rrbutani/glowing-potato/hardware/boards/pico/revA/img/pico-bottom.png

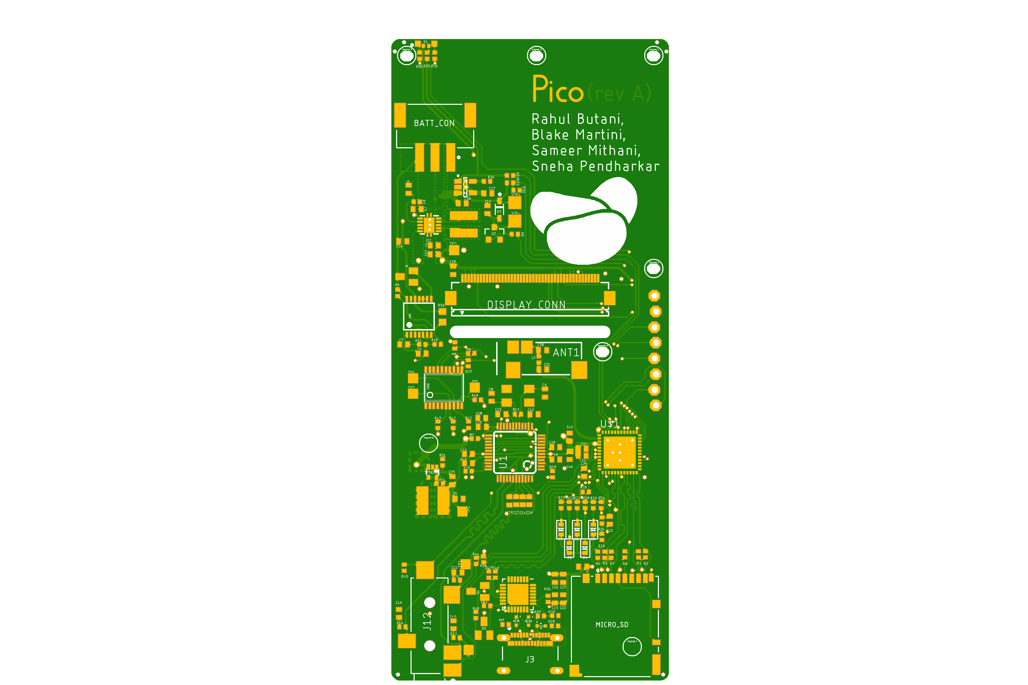
hardware/boards/pico/revA/img/pico-bottom.png
