rrbutani/glowing-potato/prototypes/buttons/buttons.asc

C1: cap; 0.1µC
R1: res; 10kR
R2: res; 50kR
R3: res; 5K
R4: res; 5kR
R5: res; 15kR
R6: res; 35k
R7: res; 75kR
R8: res; 155kR
V1: voltage; 3.3V
Named nets: 0
.tran 100
.model SW SW(Ron=1 Roff=1Meg Vt=.5 Vh=-.4)
