rrbutani/glowing-potato/prototypes/buttons/buttons2.asc

C1: cap; 0.1µC
D1: diode
D2: diode
D3: diode
D4: diode
D5: diode
D6: diode
R1: res; 10kR
R2: res; 50kR
R3: res; 5kR
R4: res; 5kR
R5: res; 15kR
R6: res; 35kR
R7: res; 75kR
R8: res; 155kR
V1: voltage; 3.3V
Named nets: 0
.tran 0.1s startup
.model SW SW(Ron=1 Roff=1Meg Vt=.5 Vh=-.4)
