rrbutani/glowing-potato/prototypes/buttons/ADC.c

// ADCSWTrigger.c
// Runs on LM4F120/TM4C123
// Provide functions that initialize ADC0 SS3 to be triggered by
// software and trigger a conversion, wait for it to finish,
// and return the result.
// Daniel Valvano
// May 2, 2015

/* This example accompanies the book
   "Embedded Systems: Real Time Interfacing to Arm Cortex M Microcontrollers",
   ISBN: 978-1463590154, Jonathan Valvano, copyright (c) 2015

 Copyright 2015 by Jonathan W. Valvano, valvano@mail.utexas.edu
    You may use, edit, run or distribute this file
    as long as the above copyright notice remains
 THIS SOFTWARE IS PROVIDED "AS IS".  NO WARRANTIES, WHETHER EXPRESS, IMPLIED
 OR STATUTORY, INCLUDING, BUT NOT LIMITED TO, IMPLIED WARRANTIES OF
 MERCHANTABILITY AND FITNESS FOR A PARTICULAR PURPOSE APPLY TO THIS SOFTWARE.
 VALVANO SHALL NOT, IN ANY CIRCUMSTANCES, BE LIABLE FOR SPECIAL, INCIDENTAL,
 OR CONSEQUENTIAL DAMAGES, FOR ANY REASON WHATSOEVER.
 For more information about my classes, my research, and my books, see
 http://users.ece.utexas.edu/~valvano/
 */
#include <stdint.h>
#include "ADCSWTrigger.h"
#include "../inc/tm4c123gh6pm.h"

// There are many choices to make when using the ADC, and many
// different combinations of settings will all do basically the
// same thing.  For simplicity, this function makes some choices
// for you.  When calling this function, be sure that it does
// not conflict with any other software that may be running on
// the microcontroller.  Particularly, ADC0 sample sequencer 3
// is used here because it only takes one sample, and only one
// sample is absolutely needed.  Sample sequencer 3 generates a
// raw interrupt when the conversion is complete, but it is not
// promoted to a controller interrupt.  Software triggers the
// ADC0 conversion and waits for the conversion to finish.  If
// somewhat precise periodic measurements are required, the
// software trigger can occur in a periodic interrupt.  This
// approach has the advantage of being simple.  However, it does
// not guarantee real-time.
//
// A better approach would be to use a hardware timer to trigger
// the ADC0 conversion independently from software and generate
// an interrupt when the conversion is finished.  Then, the
// software can transfer the conversion result to memory and
// process it after all measurements are complete.

// This initialization function sets up the ADC according to the
// following parameters.  Any parameters not explicitly listed
// below are not modified:
// Max sample rate: <=125,000 samples/second
// Sequencer 0 priority: 1st (highest)
// Sequencer 1 priority: 2nd
// Sequencer 2 priority: 3rd
// Sequencer 3 priority: 4th (lowest)
// SS3 triggering event: software trigger
// SS3 1st sample source: Ain9 (PE4)
// SS3 interrupts: enabled but not promoted to controller
void ADC0_InitSWTriggerSeq3_Ch9(void){ 
                                  // 1) activate clock for Port E
  /*uint32_t delay;
  SYSCTL_RCGCGPIO_R |= 0x10;
  while((SYSCTL_PRGPIO_R&0x10) != 0x10){};

  GPIO_PORTE_DIR_R &= ~0x10;      // 2) make PE4 input
  GPIO_PORTE_AFSEL_R |= 0x10;     // 3) enable alternate function on PE4
  GPIO_PORTE_DEN_R &= ~0x10;      // 4) disable digital I/O on PE4
  GPIO_PORTE_AMSEL_R |= 0x10;     // 5) enable analog functionality on PE4
  SYSCTL_RCGCADC_R |= 0x0001;   // 7) activate ADC0
  //while((SYSCTL_PRADC_R&0x0001) != 0x0001){};    // good code, but not yet implemented in simulator
  delay = 42;
  ADC0_PC_R &= ~0xF;              // 7) clear max sample rate field
  ADC0_PC_R |= 0x1;               //    configure for 125K samples/sec
  ADC0_SSPRI_R = 0x0123;          // 8) Sequencer 3 is highest priority
  ADC0_ACTSS_R &= ~0x0008;        // 9) disable sample sequencer 3
  ADC0_EMUX_R &= ~0xF000;         // 10) seq3 is software trigger
  ADC0_SSMUX3_R &= ~0x000F;       // 11) clear SS3 field
  ADC0_SSMUX3_R += 9;             //    set channel
  ADC0_SSCTL3_R = 0x0006;         // 12) no TS0 D0, yes IE0 END0
  ADC0_IM_R &= ~0x0008;           // 13) disable SS3 interrupts
  ADC0_ACTSS_R |= 0x0008;         // 14) enable sample sequencer 3*/
  
  uint32_t delay;
  SYSCTL_RCGCGPIO_R |= 0x00000010;   // 1) activate clock for Port E
  delay = SYSCTL_RCGC2_R;         //    allow time for clock to stabilize
  GPIO_PORTE_DIR_R &= ~0x04;      // 2) make PE4 input
  GPIO_PORTE_AFSEL_R |= 0x04;     // 3) enable alternate function on PE2
  GPIO_PORTE_DEN_R &= ~0x04;      // 4) disable digital I/O on PE2
  GPIO_PORTE_AMSEL_R |= 0x04;     // 5) enable analog function on PE2
  SYSCTL_RCGC0_R |= 0x00010000;   // 6) activate ADC0
  delay = SYSCTL_RCGC2_R;        
  SYSCTL_RCGC0_R &= ~0x00000300;  // 7) configure for 125K
  ADC0_SSPRI_R = 0x0123;          // 8) Sequencer 3 is highest priority
  ADC0_ACTSS_R &= ~0x0008;        // 9) disable sample sequencer 3
  ADC0_EMUX_R &= ~0xF000;         // 10) seq3 is software trigger
  ADC0_SSMUX3_R &= ~0x000F;       // 11) clear SS3 field
  ADC0_SSMUX3_R += 9;             //    set channel Ain9 (PE4)
  ADC0_SSCTL3_R = 0x0006;         // 12) no TS0 D0, yes IE0 END0
  ADC0_ACTSS_R |= 0x0008;         // 13) enable sample sequencer 3
}

//------------ADC0_InSeq3------------
// Busy-wait Analog to digital conversion
// Input: none
// Output: 12-bit result of ADC conversion
uint32_t ADC0_InSeq3(void){  uint32_t result;
  ADC0_PSSI_R = 0x0008;            // 1) initiate SS3
  while((ADC0_RIS_R&0x08)==0){};   // 2) wait for conversion done
    // if you have an A0-A3 revision number, you need to add an 8 usec wait here
  result = ADC0_SSFIFO3_R&0xFFF;   // 3) read result
  ADC0_ISC_R = 0x0008;             // 4) acknowledge completion
  return result;
}
